Orange-OpenSource/iotContinuum/DevKit-HL7812/Arduino/examples/SwitchHL7812/README.md

# IoT Continuum

This page is part of the [IoT Continuum Dev Kit](/) / [Arduino](/Arduino) section

<picture>
 <source media="(prefers-color-scheme: dark)" srcset="/images/DevKit_face1-black.jpg">
 <source media="(prefers-color-scheme: light)" srcset="/images/DevKit_face1-white.jpg">
 IoT Continuum Dev Kit
</picture>

# Switch HL7812

[This sample code](SwitchHL7812.ino) shows how to use of the devkit switch: once the program running, press the User Button on the board to switch to HL7812. You can then pass AT commands to the HL7812.
