Orange-OpenSource/iotContinuum/DevKit-HL7812/Zephyr/devkit-iot-continuum/demo_devkit_iot_continuum/app_main/README.rst

.. demo_devkit:

Demo DevKit IOT Continuum
#########################

Overview
********

The purpose of this example is to show all the component's basic capability on the DevKit IOT Continuum board (HL7812 Modem, LSM6DSO and BME280)

The demo start with a LED example which turn on/off all the LED.

Then it will use the BME280 module BSP which allows to retrieve and display pression, temperature and humidity data. 

Then it will use the LSM6DSO module BSP which allows to retrieve and display rotation and acceleration data.

At the end, it will use the Modem BSP to create a HTTP connection on www.google.com and ping it.

Build & Run
***********

Requirements
============

Have a SIM card inserted in the DevKit IOT Continuum board.

Build
=====

.. code-block:: bash

   $ cd $(west topdir)/devkit-iot-continuum
   $ west build -b devkit_iot_continuum demo_devkit_iot_continuum/ -p

Run
===

.. code-block:: bash

   $ west flash

Output
======

USB Modem
_________

.. note::
   Output for devkit_iot_continuum board with SIM card

.. code-block:: bash

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
