Orange-OpenSource/iotContinuum/DevKit-HL7812/images/DevKit_face1-black.jpg

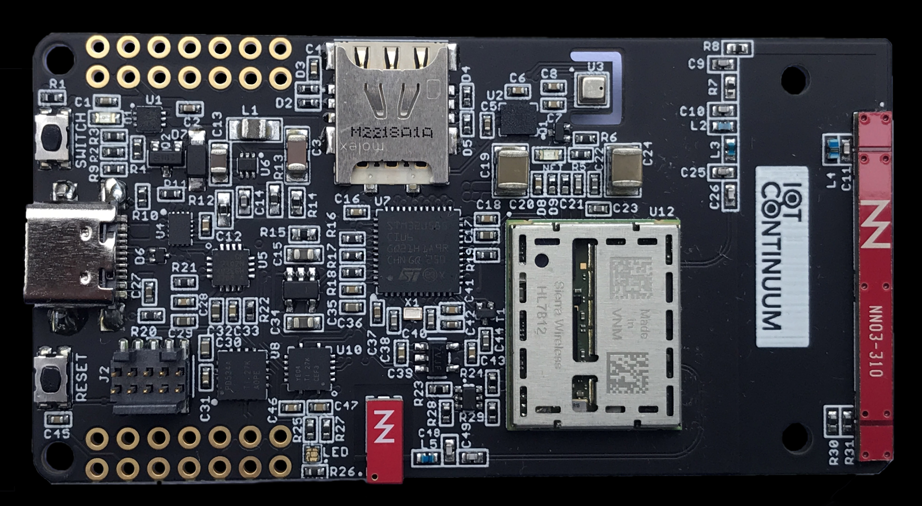
DevKit-HL7812/images/DevKit_face1-black.jpg
