Orange-OpenSource/iotContinuum/DevKit-HL7812/images/DevKit_face2-black.jpg

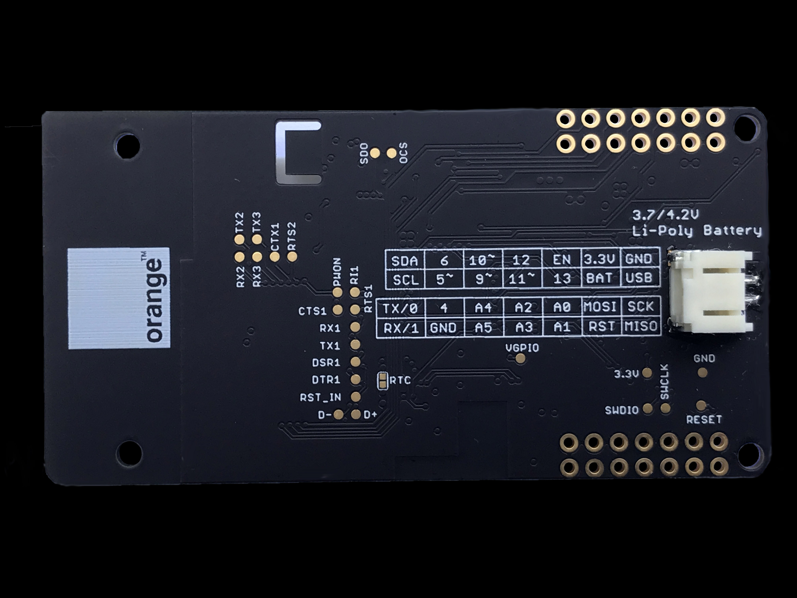
DevKit-HL7812/images/DevKit_face2-black.jpg
