Orange-OpenSource/iotContinuum/DevKit-HL7812/images/DevKit_face2-white.jpg

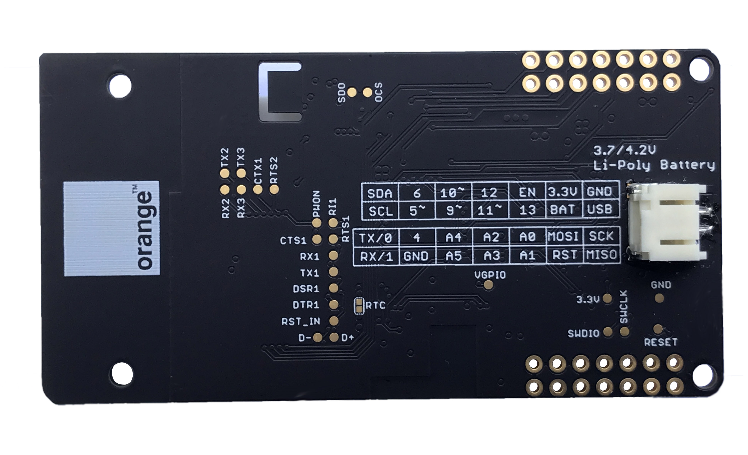
DevKit-HL7812/images/DevKit_face2-white.jpg
