Orange-OpenSource/iotContinuum/images/devkit_general.png

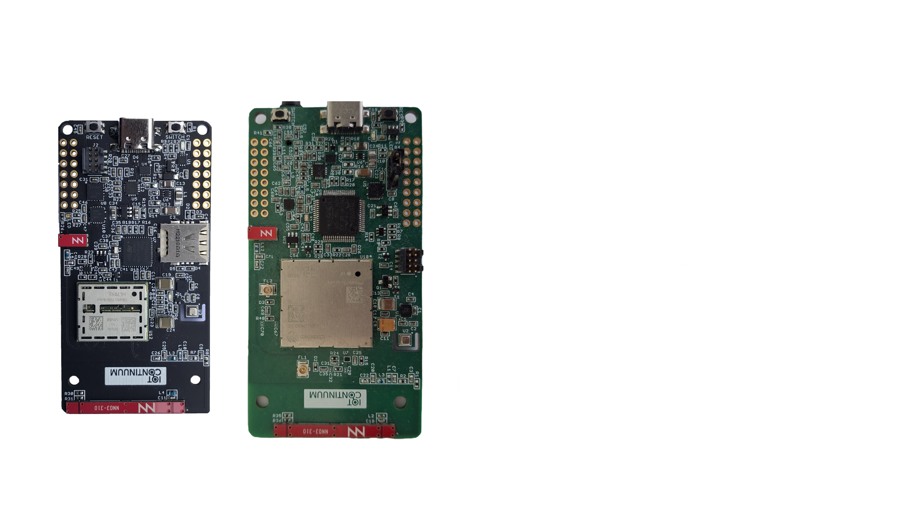
images/devkit_general.png
