Orange-OpenSource/iotContinuum/DevKit-RC7620/Arduino/core/U575R(G-I)T_U585RIT/PeripheralPins_IOT_CONTINUUM_DEVKIT.c

/*
 *******************************************************************************
 * Copyright (c) 2020, STMicroelectronics
 * All rights reserved.
 *
 * This software component is licensed by ST under BSD 3-Clause license,
 * the "License"; You may not use this file except in compliance with the
 * License. You may obtain a copy of the License at:
 *                        opensource.org/licenses/BSD-3-Clause
 *
 *******************************************************************************
 */
/*
 * Automatically generated from STM32U575CGTx.xml, STM32U575CGUx.xml
 * STM32U575CITx.xml, STM32U575CIUx.xml
 * STM32U585CITx.xml, STM32U585CIUx.xml
 * CubeMX DB release 6.0.90
 */
#if defined(ARDUINO_IOT_CONTINUUM_DEVKIT2)
#include "Arduino.h"
#include "PeripheralPins.h"

/* =====
 * Notes:
 * - The pins mentioned Px_y_ALTz are alternative possibilities which use other
 *   HW peripheral instances. You can use them the same way as any other "normal"
 *   pin (i.e. analogWrite(PA7_ALT1, 128);).
 *
 * - Commented lines are alternative possibilities which are not used per default.
 *   If you change them, you will have to know what you do
 * =====
 */

//*** ADC ***

#ifdef HAL_ADC_MODULE_ENABLED
WEAK const PinMap PinMap_ADC[] = {
  {PA_0,      ADC1, STM_PIN_DATA_EXT(STM_MODE_ANALOG, GPIO_NOPULL, 0, 5, 0)}, // ADC1_IN5
  {PA_1,      ADC1, STM_PIN_DATA_EXT(STM_MODE_ANALOG, GPIO_NOPULL, 0, 6, 0)}, // ADC1_IN6
  {PA_4,      ADC1, STM_PIN_DATA_EXT(STM_MODE_ANALOG, GPIO_NOPULL, 0, 9, 0)}, // ADC1_IN9
  {PA_4_ALT1, ADC4, STM_PIN_DATA_EXT(STM_MODE_ANALOG, GPIO_NOPULL, 0, 9, 0)}, // ADC4_IN9
  {PA_6,      ADC1, STM_PIN_DATA_EXT(STM_MODE_ANALOG, GPIO_NOPULL, 0, 11, 0)}, // ADC1_IN11
  {PA_6_ALT1, ADC4, STM_PIN_DATA_EXT(STM_MODE_ANALOG, GPIO_NOPULL, 0, 11, 0)}, // ADC4_IN11
  {PB_0,      ADC1, STM_PIN_DATA_EXT(STM_MODE_ANALOG, GPIO_NOPULL, 0, 15, 0)}, // ADC1_IN15
  {PB_0_ALT1, ADC4, STM_PIN_DATA_EXT(STM_MODE_ANALOG, GPIO_NOPULL, 0, 18, 0)}, // ADC4_IN18
  {PB_1,      ADC1, STM_PIN_DATA_EXT(STM_MODE_ANALOG, GPIO_NOPULL, 0, 16, 0)}, // ADC1_IN16
  {PB_1_ALT1, ADC4, STM_PIN_DATA_EXT(STM_MODE_ANALOG, GPIO_NOPULL, 0, 19, 0)}, // ADC4_IN19
  {PB_2,      ADC1, STM_PIN_DATA_EXT(STM_MODE_ANALOG, GPIO_NOPULL, 0, 17, 0)}, // ADC1_IN17
  {NC,        NP,   0}
};
#endif

//*** DAC ***

#ifdef HAL_DAC_MODULE_ENABLED
WEAK const PinMap PinMap_DAC[] = {
  {PA_4, DAC1, STM_PIN_DATA_EXT(STM_MODE_ANALOG, GPIO_NOPULL, 0, 1, 0)}, // DAC1_OUT1
  {PA_5, DAC1, STM_PIN_DATA_EXT(STM_MODE_ANALOG, GPIO_NOPULL, 0, 2, 0)}, // DAC1_OUT2
  {NC,   NP,   0}
};
#endif

//*** I2C ***

#ifdef HAL_I2C_MODULE_ENABLED
WEAK const PinMap PinMap_I2C_SDA[] = {
  {PB_7,      I2C4, STM_PIN_DATA(STM_MODE_AF_OD, GPIO_NOPULL, GPIO_AF5_I2C4)},
  {PB_14,     I2C2, STM_PIN_DATA(STM_MODE_AF_OD, GPIO_NOPULL, GPIO_AF4_I2C2)},
  {NC,        NP,   0}
};
#endif

#ifdef HAL_I2C_MODULE_ENABLED
WEAK const PinMap PinMap_I2C_SCL[] = {
  {PB_6,       I2C4, STM_PIN_DATA(STM_MODE_AF_OD, GPIO_NOPULL, GPIO_AF5_I2C4)},
  {PB_10,      I2C2, STM_PIN_DATA(STM_MODE_AF_OD, GPIO_NOPULL, GPIO_AF4_I2C2)},
  {PB_13,      I2C2, STM_PIN_DATA(STM_MODE_AF_OD, GPIO_NOPULL, GPIO_AF4_I2C2)},
  {NC,         NP,   0}
};
#endif

//*** No I3C ***

//*** TIM ***

#ifdef HAL_TIM_MODULE_ENABLED
WEAK const PinMap PinMap_TIM[] = {
  {PA_0,       TIM2,  STM_PIN_DATA_EXT(STM_MODE_AF_PP, GPIO_PULLUP, GPIO_AF1_TIM2, 1, 0)}, // TIM2_CH1
  {PA_0_ALT1,  TIM5,  STM_PIN_DATA_EXT(STM_MODE_AF_PP, GPIO_PULLUP, GPIO_AF2_TIM5, 1, 0)}, // TIM5_CH1
  {PA_1,       TIM2,  STM_PIN_DATA_EXT(STM_MODE_AF_PP, GPIO_PULLUP, GPIO_AF1_TIM2, 2, 0)}, // TIM2_CH2
  {PA_1_ALT1,  TIM5,  STM_PIN_DATA_EXT(STM_MODE_AF_PP, GPIO_PULLUP, GPIO_AF2_TIM5, 2, 0)}, // TIM5_CH2
  {PA_1_ALT2,  TIM15, STM_PIN_DATA_EXT(STM_MODE_AF_PP, GPIO_PULLUP, GPIO_AF14_TIM15, 1, 1)}, // TIM15_CH1N
  {PA_2,       TIM2,  STM_PIN_DATA_EXT(STM_MODE_AF_PP, GPIO_PULLUP, GPIO_AF1_TIM2, 3, 0)}, // TIM2_CH3
  {PA_2_ALT1,  TIM5,  STM_PIN_DATA_EXT(STM_MODE_AF_PP, GPIO_PULLUP, GPIO_AF2_TIM5, 3, 0)}, // TIM5_CH3
  {PA_2_ALT2,  TIM15, STM_PIN_DATA_EXT(STM_MODE_AF_PP, GPIO_PULLUP, GPIO_AF14_TIM15, 1, 0)}, // TIM15_CH1
  {PA_3,       TIM2,  STM_PIN_DATA_EXT(STM_MODE_AF_PP, GPIO_PULLUP, GPIO_AF1_TIM2, 4, 0)}, // TIM2_CH4
  {PA_3_ALT1,  TIM5,  STM_PIN_DATA_EXT(STM_MODE_AF_PP, GPIO_PULLUP, GPIO_AF2_TIM5, 4, 0)}, // TIM5_CH4
  {PA_3_ALT2,  TIM15, STM_PIN_DATA_EXT(STM_MODE_AF_PP, GPIO_PULLUP, GPIO_AF14_TIM15, 2, 0)}, // TIM15_CH2
  {PA_6,       TIM3,  STM_PIN_DATA_EXT(STM_MODE_AF_PP, GPIO_PULLUP, GPIO_AF2_TIM3, 1, 0)}, // TIM3_CH1
  {PA_6_ALT1,  TIM16, STM_PIN_DATA_EXT(STM_MODE_AF_PP, GPIO_PULLUP, GPIO_AF14_TIM16, 1, 0)}, // TIM16_CH1
  {PA_8,       TIM1,  STM_PIN_DATA_EXT(STM_MODE_AF_PP, GPIO_PULLUP, GPIO_AF1_TIM1, 1, 0)}, // TIM1_CH1
  {PA_9,       TIM1,  STM_PIN_DATA_EXT(STM_MODE_AF_PP, GPIO_PULLUP, GPIO_AF1_TIM1, 2, 0)}, // TIM1_CH2
  {PA_10,      TIM1,  STM_PIN_DATA_EXT(STM_MODE_AF_PP, GPIO_PULLUP, GPIO_AF1_TIM1, 3, 0)}, // TIM1_CH3
  {PA_11,      TIM1,  STM_PIN_DATA_EXT(STM_MODE_AF_PP, GPIO_PULLUP, GPIO_AF1_TIM1, 4, 0)}, // TIM1_CH4
  {PB_0,       TIM1,  STM_PIN_DATA_EXT(STM_MODE_AF_PP, GPIO_PULLUP, GPIO_AF1_TIM1, 2, 1)}, // TIM1_CH2N
  {PB_0_ALT1,  TIM3,  STM_PIN_DATA_EXT(STM_MODE_AF_PP, GPIO_PULLUP, GPIO_AF2_TIM3, 3, 0)}, // TIM3_CH3
  {PB_0_ALT2,  TIM8,  STM_PIN_DATA_EXT(STM_MODE_AF_PP, GPIO_PULLUP, GPIO_AF3_TIM8, 2, 1)}, // TIM8_CH2N
  {PB_1,       TIM1,  STM_PIN_DATA_EXT(STM_MODE_AF_PP, GPIO_PULLUP, GPIO_AF1_TIM1, 3, 1)}, // TIM1_CH3N
  {PB_1_ALT1,  TIM3,  STM_PIN_DATA_EXT(STM_MODE_AF_PP, GPIO_PULLUP, GPIO_AF2_TIM3, 4, 0)}, // TIM3_CH4
  {PB_1_ALT2,  TIM8,  STM_PIN_DATA_EXT(STM_MODE_AF_PP, GPIO_PULLUP, GPIO_AF3_TIM8, 3, 1)}, // TIM8_CH3N
  {PB_2,       TIM8,  STM_PIN_DATA_EXT(STM_MODE_AF_PP, GPIO_PULLUP, GPIO_AF3_TIM8, 4, 1)}, // TIM8_CH4N
  {PB_3,       TIM2,  STM_PIN_DATA_EXT(STM_MODE_AF_PP, GPIO_PULLUP, GPIO_AF1_TIM2, 2, 0)}, // TIM2_CH2
  {PB_4,       TIM3,  STM_PIN_DATA_EXT(STM_MODE_AF_PP, GPIO_PULLUP, GPIO_AF2_TIM3, 1, 0)}, // TIM3_CH1
  {PB_5,       TIM3,  STM_PIN_DATA_EXT(STM_MODE_AF_PP, GPIO_PULLUP, GPIO_AF2_TIM3, 2, 0)}, // TIM3_CH2
  {PB_10,      TIM2,  STM_PIN_DATA_EXT(STM_MODE_AF_PP, GPIO_PULLUP, GPIO_AF1_TIM2, 3, 0)}, // TIM2_CH3
  {PB_13,      TIM1,  STM_PIN_DATA_EXT(STM_MODE_AF_PP, GPIO_PULLUP, GPIO_AF1_TIM1, 1, 1)}, // TIM1_CH1N
  {PB_13_ALT1, TIM15, STM_PIN_DATA_EXT(STM_MODE_AF_PP, GPIO_PULLUP, GPIO_AF14_TIM15, 1, 1)}, // TIM15_CH1N
  {PB_14,      TIM1,  STM_PIN_DATA_EXT(STM_MODE_AF_PP, GPIO_PULLUP, GPIO_AF1_TIM1, 2, 1)}, // TIM1_CH2N
  {PB_14_ALT1, TIM8,  STM_PIN_DATA_EXT(STM_MODE_AF_PP, GPIO_PULLUP, GPIO_AF3_TIM8, 2, 1)}, // TIM8_CH2N
  {PB_14_ALT2, TIM15, STM_PIN_DATA_EXT(STM_MODE_AF_PP, GPIO_PULLUP, GPIO_AF14_TIM15, 1, 0)}, // TIM15_CH1
  {PB_15,      TIM1,  STM_PIN_DATA_EXT(STM_MODE_AF_PP, GPIO_PULLUP, GPIO_AF1_TIM1, 3, 1)}, // TIM1_CH3N
  {PB_15_ALT1, TIM8,  STM_PIN_DATA_EXT(STM_MODE_AF_PP, GPIO_PULLUP, GPIO_AF3_TIM8, 3, 1)}, // TIM8_CH3N
  {PB_15_ALT2, TIM15, STM_PIN_DATA_EXT(STM_MODE_AF_PP, GPIO_PULLUP, GPIO_AF14_TIM15, 2, 0)}, // TIM15_CH2
  {NC,         NP,    0}
};
#endif

//*** UART ***

#ifdef HAL_UART_MODULE_ENABLED
WEAK const PinMap PinMap_UART_TX[] = {
  {PA_0,      UART4,   STM_PIN_DATA(STM_MODE_AF_PP, GPIO_PULLUP, GPIO_AF8_UART4)},
  {PA_2,      LPUART1, STM_PIN_DATA(STM_MODE_AF_PP, GPIO_PULLUP, GPIO_AF8_LPUART1)},
  {PA_7,      USART3,  STM_PIN_DATA(STM_MODE_AF_PP, GPIO_PULLUP, GPIO_AF7_USART3)},
  {PA_9,      USART1,  STM_PIN_DATA(STM_MODE_AF_PP, GPIO_PULLUP, GPIO_AF7_USART1)},
  {PB_10,     USART3,  STM_PIN_DATA(STM_MODE_AF_PP, GPIO_PULLUP, GPIO_AF7_USART3)},
  {NC,        NP,      0}
};
#endif

#ifdef HAL_UART_MODULE_ENABLED
WEAK const PinMap PinMap_UART_RX[] = {
  {PA_1,      UART4,   STM_PIN_DATA(STM_MODE_AF_PP, GPIO_PULLUP, GPIO_AF8_UART4)},
  {PA_3,      LPUART1, STM_PIN_DATA(STM_MODE_AF_PP, GPIO_PULLUP, GPIO_AF8_LPUART1)},
  {PA_5,      USART3,  STM_PIN_DATA(STM_MODE_AF_PP, GPIO_PULLUP, GPIO_AF7_USART3)},
  {PA_10,     USART1,  STM_PIN_DATA(STM_MODE_AF_PP, GPIO_PULLUP, GPIO_AF7_USART1)},
  {PB_10,     LPUART1, STM_PIN_DATA(STM_MODE_AF_PP, GPIO_PULLUP, GPIO_AF8_LPUART1)},
  {NC,        NP,      0}
};
#endif

#ifdef HAL_UART_MODULE_ENABLED
WEAK const PinMap PinMap_UART_RTS[] = {
  {PB_1,       LPUART1, STM_PIN_DATA(STM_MODE_AF_PP, GPIO_PULLUP, GPIO_AF8_LPUART1)},
  {PB_1_ALT1,  USART3,  STM_PIN_DATA(STM_MODE_AF_PP, GPIO_PULLUP, GPIO_AF7_USART3)},
  {PB_3,       USART1,  STM_PIN_DATA(STM_MODE_AF_PP, GPIO_PULLUP, GPIO_AF7_USART1)},
  {PB_14,      USART3,  STM_PIN_DATA(STM_MODE_AF_PP, GPIO_PULLUP, GPIO_AF7_USART3)},
  {NC,         NP,      0}
};
#endif

#ifdef HAL_UART_MODULE_ENABLED
WEAK const PinMap PinMap_UART_CTS[] = {
  {PA_6,       LPUART1, STM_PIN_DATA(STM_MODE_AF_PP, GPIO_PULLUP, GPIO_AF8_LPUART1)},
  {PA_6_ALT1,  USART3,  STM_PIN_DATA(STM_MODE_AF_PP, GPIO_PULLUP, GPIO_AF7_USART3)},
  {PA_11,      USART1,  STM_PIN_DATA(STM_MODE_AF_PP, GPIO_PULLUP, GPIO_AF7_USART1)},
  {PB_4,       USART1,  STM_PIN_DATA(STM_MODE_AF_PP, GPIO_PULLUP, GPIO_AF7_USART1)},
  {PB_7,       UART4,   STM_PIN_DATA(STM_MODE_AF_PP, GPIO_PULLUP, GPIO_AF8_UART4)},
  {PB_13,      LPUART1, STM_PIN_DATA(STM_MODE_AF_PP, GPIO_PULLUP, GPIO_AF8_LPUART1)},
  {PB_13_ALT1, USART3,  STM_PIN_DATA(STM_MODE_AF_PP, GPIO_PULLUP, GPIO_AF7_USART3)},
  {NC,         NP,      0}
};
#endif

//*** SPI ***

#ifdef HAL_SPI_MODULE_ENABLED
WEAK const PinMap PinMap_SPI_MOSI[] = {
  {PB_5,      SPI1, STM_PIN_DATA(STM_MODE_AF_PP, GPIO_PULLUP, GPIO_AF5_SPI1)},
  {PB_5_ALT1, SPI3, STM_PIN_DATA(STM_MODE_AF_PP, GPIO_PULLUP, GPIO_AF6_SPI3)},
  {PB_15,     SPI2, STM_PIN_DATA(STM_MODE_AF_PP, GPIO_PULLUP, GPIO_AF5_SPI2)},
  {NC,        NP,   0}
};
#endif

#ifdef HAL_SPI_MODULE_ENABLED
WEAK const PinMap PinMap_SPI_MISO[] = {
  {PA_11,     SPI1, STM_PIN_DATA(STM_MODE_AF_PP, GPIO_PULLUP, GPIO_AF5_SPI1)},
  {PB_4,      SPI1, STM_PIN_DATA(STM_MODE_AF_PP, GPIO_PULLUP, GPIO_AF5_SPI1)},
  {PB_4_ALT1, SPI3, STM_PIN_DATA(STM_MODE_AF_PP, GPIO_PULLUP, GPIO_AF6_SPI3)},
  {PB_14,     SPI2, STM_PIN_DATA(STM_MODE_AF_PP, GPIO_PULLUP, GPIO_AF5_SPI2)},
  {NC,        NP,   0}
};
#endif

#ifdef HAL_SPI_MODULE_ENABLED
WEAK const PinMap PinMap_SPI_SCLK[] = {
  {PA_1,      SPI1, STM_PIN_DATA(STM_MODE_AF_PP, GPIO_PULLUP, GPIO_AF5_SPI1)},
  {PB_3,      SPI1, STM_PIN_DATA(STM_MODE_AF_PP, GPIO_PULLUP, GPIO_AF5_SPI1)},
  {PB_3_ALT1, SPI3, STM_PIN_DATA(STM_MODE_AF_PP, GPIO_PULLUP, GPIO_AF6_SPI3)},
  {PB_10,     SPI2, STM_PIN_DATA(STM_MODE_AF_PP, GPIO_PULLUP, GPIO_AF5_SPI2)},
  {PB_13,     SPI2, STM_PIN_DATA(STM_MODE_AF_PP, GPIO_PULLUP, GPIO_AF5_SPI2)},
  {NC,        NP,   0}
};
#endif

#ifdef HAL_SPI_MODULE_ENABLED
WEAK const PinMap PinMap_SPI_SSEL[] = {
  {PB_0,       SPI1, STM_PIN_DATA(STM_MODE_AF_PP, GPIO_PULLUP, GPIO_AF5_SPI1)},
  {NC,         NP,   0}
};
#endif

//*** FDCAN ***

#ifdef HAL_FDCAN_MODULE_ENABLED
WEAK const PinMap PinMap_CAN_RD[] = {
  {PA_11, FDCAN1, STM_PIN_DATA(STM_MODE_AF_PP, GPIO_NOPULL, GPIO_AF9_FDCAN1)},
  {PB_8,  FDCAN1, STM_PIN_DATA(STM_MODE_AF_PP, GPIO_NOPULL, GPIO_AF9_FDCAN1)},
  {NC,    NP,     0}
};
#endif

#ifdef HAL_FDCAN_MODULE_ENABLED
WEAK const PinMap PinMap_CAN_TD[] = {
  {PA_12, FDCAN1, STM_PIN_DATA(STM_MODE_AF_PP, GPIO_NOPULL, GPIO_AF9_FDCAN1)},
  {PB_9,  FDCAN1, STM_PIN_DATA(STM_MODE_AF_PP, GPIO_NOPULL, GPIO_AF9_FDCAN1)},
  {NC,    NP,     0}
};
#endif

//*** No ETHERNET ***

//*** OCTOSPI ***

#ifdef HAL_OSPI_MODULE_ENABLED
WEAK const PinMap PinMap_OCTOSPI_DATA0[] = {
  {PB_1, OCTOSPI1, STM_PIN_DATA(STM_MODE_AF_PP, GPIO_PULLUP, GPIO_AF10_OCTOSPI1)}, // OCTOSPIM_P1_IO0
  {NC,   NP,       0}
};
#endif

#ifdef HAL_OSPI_MODULE_ENABLED
WEAK const PinMap PinMap_OCTOSPI_DATA1[] = {
  {PB_0, OCTOSPI1, STM_PIN_DATA(STM_MODE_AF_PP, GPIO_PULLUP, GPIO_AF10_OCTOSPI1)}, // OCTOSPIM_P1_IO1
  {NC,   NP,       0}
};
#endif

#ifdef HAL_OSPI_MODULE_ENABLED
WEAK const PinMap PinMap_OCTOSPI_DATA2[] = {
  {PA_7, OCTOSPI1, STM_PIN_DATA(STM_MODE_AF_PP, GPIO_PULLUP, GPIO_AF10_OCTOSPI1)}, // OCTOSPIM_P1_IO2
  {NC,   NP,       0}
};
#endif

#ifdef HAL_OSPI_MODULE_ENABLED
WEAK const PinMap PinMap_OCTOSPI_DATA3[] = {
  {PA_6, OCTOSPI1, STM_PIN_DATA(STM_MODE_AF_PP, GPIO_PULLUP, GPIO_AF10_OCTOSPI1)}, // OCTOSPIM_P1_IO3
  {NC,   NP,       0}
};
#endif

#ifdef HAL_OSPI_MODULE_ENABLED
WEAK const PinMap PinMap_OCTOSPI_SCLK[] = {
  {PA_3,  OCTOSPI1, STM_PIN_DATA(STM_MODE_AF_PP, GPIO_PULLUP, GPIO_AF10_OCTOSPI1)}, // OCTOSPIM_P1_CLK
  {PB_10, OCTOSPI1, STM_PIN_DATA(STM_MODE_AF_PP, GPIO_PULLUP, GPIO_AF10_OCTOSPI1)}, // OCTOSPIM_P1_CLK
  {NC,    NP,       0}
};
#endif

#ifdef HAL_OSPI_MODULE_ENABLED
WEAK const PinMap PinMap_OCTOSPI_SSEL[] = {
  {PA_0,  OCTOSPI2, STM_PIN_DATA(STM_MODE_AF_PP, GPIO_PULLUP, GPIO_AF10_OCTOSPI2)}, // OCTOSPIM_P2_NCS
  {PA_2,  OCTOSPI1, STM_PIN_DATA(STM_MODE_AF_PP, GPIO_PULLUP, GPIO_AF10_OCTOSPI1)}, // OCTOSPIM_P1_NCS
  {PA_4,  OCTOSPI1, STM_PIN_DATA(STM_MODE_AF_PP, GPIO_PULLUP, GPIO_AF3_OCTOSPI1)}, // OCTOSPIM_P1_NCS
  {PA_12, OCTOSPI2, STM_PIN_DATA(STM_MODE_AF_PP, GPIO_PULLUP, GPIO_AF6_OCTOSPI2)}, // OCTOSPIM_P2_NCS
  {NC,    NP,       0}
};
#endif

//*** USB ***

#if defined(HAL_PCD_MODULE_ENABLED) || defined(HAL_HCD_MODULE_ENABLED)
WEAK const PinMap PinMap_USB_OTG_FS[] = {
  {PA_8,  USB_OTG_FS, STM_PIN_DATA(STM_MODE_AF_PP, GPIO_PULLUP, GPIO_AF10_USB)}, // USB_OTG_FS_SOF
  {PA_9,  USB_OTG_FS, STM_PIN_DATA(STM_MODE_INPUT, GPIO_NOPULL, GPIO_AF_NONE)}, // USB_OTG_FS_VBUS
  {PA_10, USB_OTG_FS, STM_PIN_DATA(STM_MODE_AF_OD, GPIO_PULLUP, GPIO_AF10_USB)}, // USB_OTG_FS_ID
  {PA_11, USB_OTG_FS, STM_PIN_DATA(STM_MODE_AF_PP, GPIO_PULLUP, GPIO_AF10_USB)}, // USB_OTG_FS_DM
  {PA_12, USB_OTG_FS, STM_PIN_DATA(STM_MODE_AF_PP, GPIO_PULLUP, GPIO_AF10_USB)}, // USB_OTG_FS_DP
  {PA_13, USB_OTG_FS, STM_PIN_DATA(STM_MODE_AF_PP, GPIO_PULLUP, GPIO_AF10_USB)}, // USB_OTG_FS_NOE
  {PA_14, USB_OTG_FS, STM_PIN_DATA(STM_MODE_AF_PP, GPIO_PULLUP, GPIO_AF10_USB)}, // USB_OTG_FS_SOF
  {NC,    NP,         0}
};
#endif

//*** No SD ***

#endif /* ARDUINO_DEVKIT_IOT_CONTINUUM */
